edcorreamo/Mocap/Esquematico/Esquematico_completo_page-0001.jpg

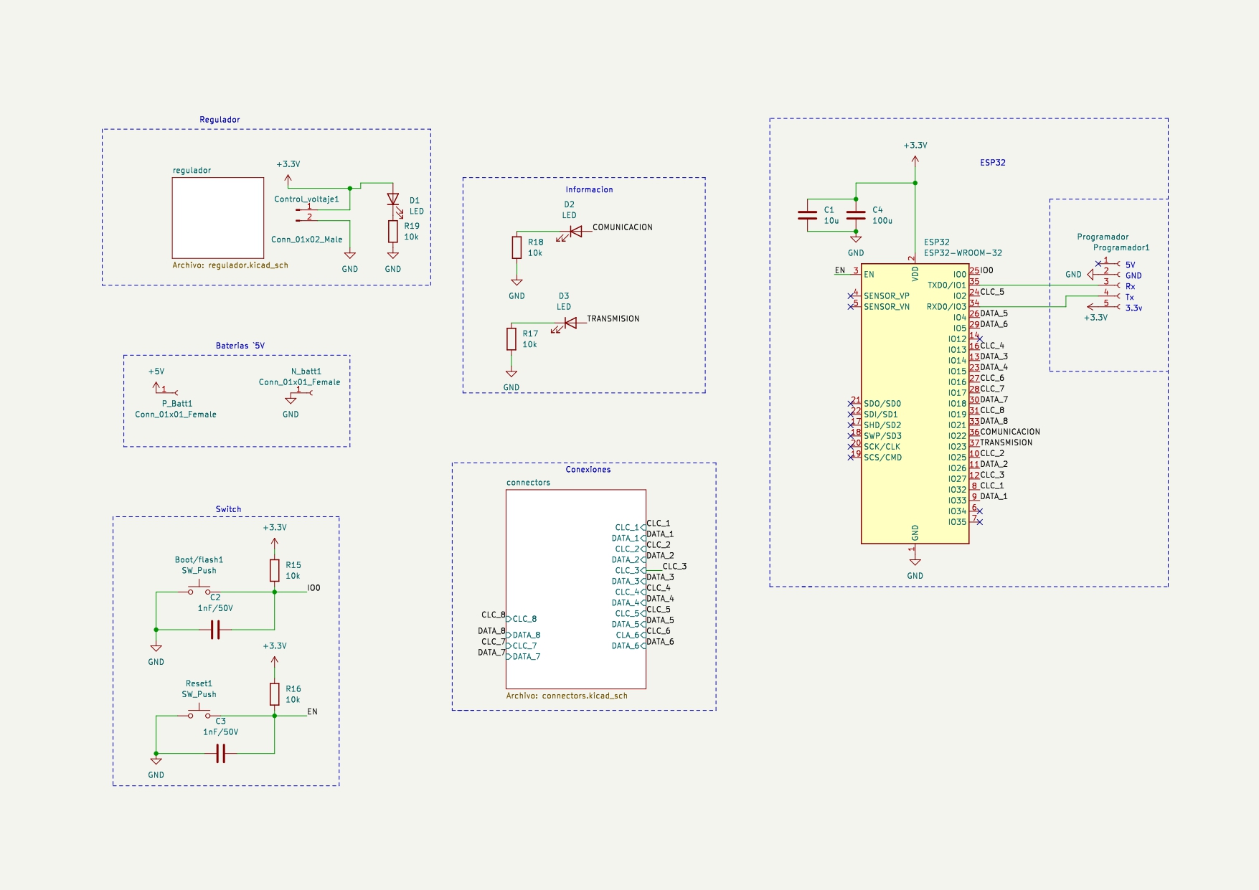
Esquematico/Esquematico_completo_page-0001.jpg
