edcorreamo/Mocap/Esquematico/Esquematico_completo_page-0002.jpg

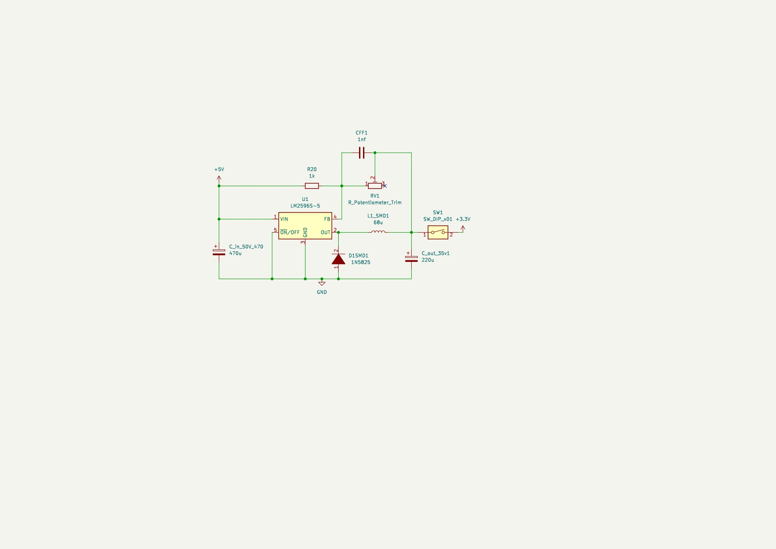
Esquematico/Esquematico_completo_page-0002.jpg
