edcorreamo/Mocap/Esquematico/Esquematico_completo_page-0003.jpg

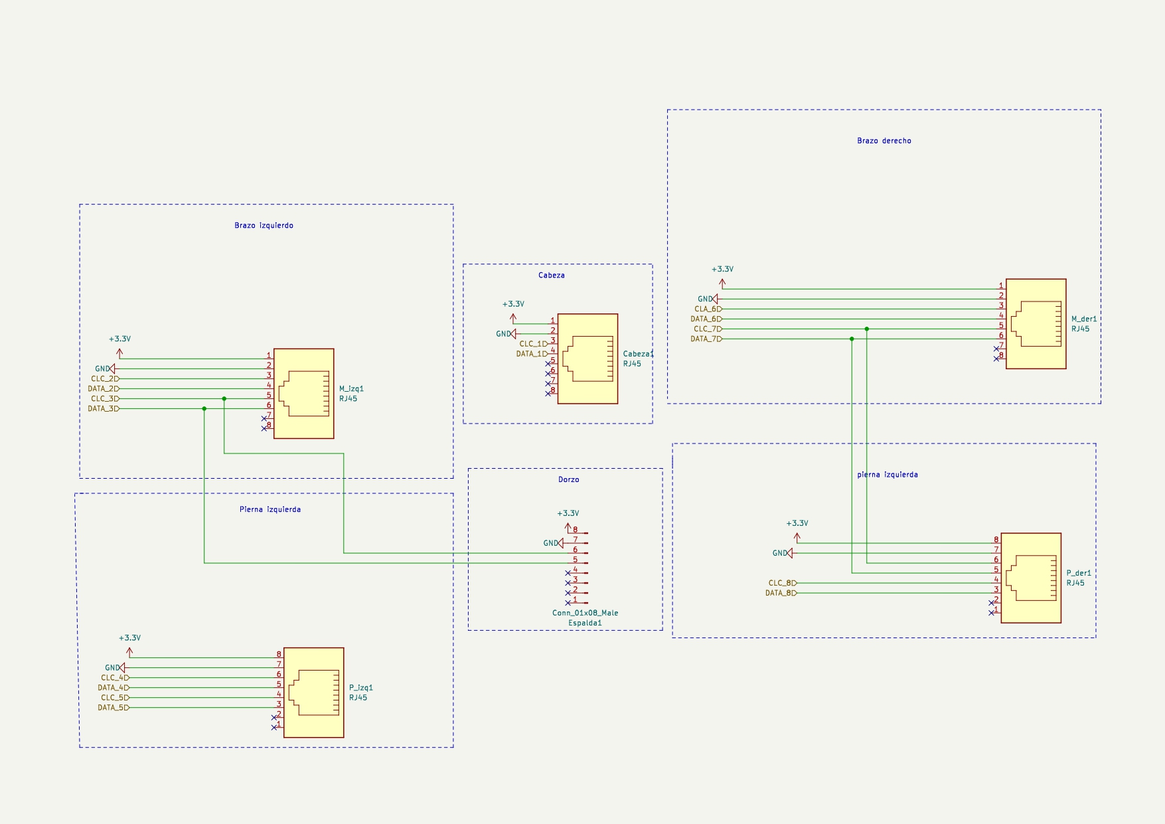
Esquematico/Esquematico_completo_page-0003.jpg
