edcorreamo/Mocap/imagenes/Base2.JPG

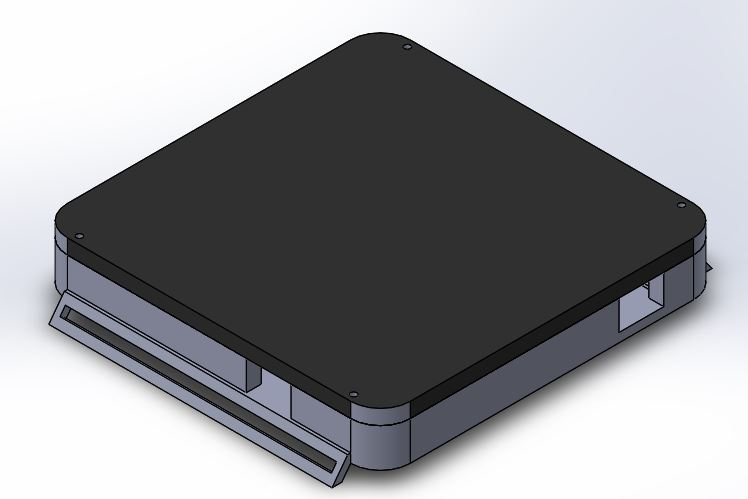
imagenes/Base2.JPG
