edcorreamo/Mocap/imagenes/Base.JPG

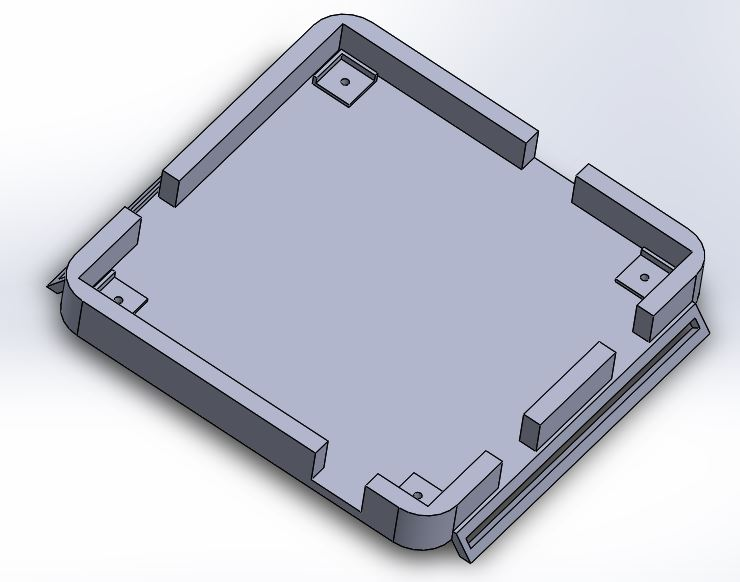
imagenes/Base.JPG
