edcorreamo/Mocap/imagenes/conector.PNG

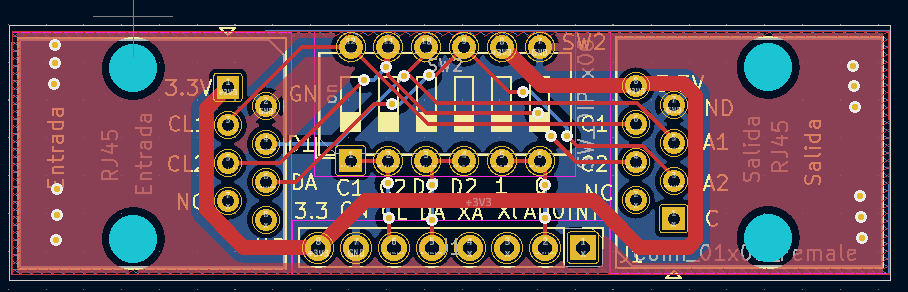
imagenes/conector.PNG
