edcorreamo/Mocap/imagenes/conector_2_3D.PNG

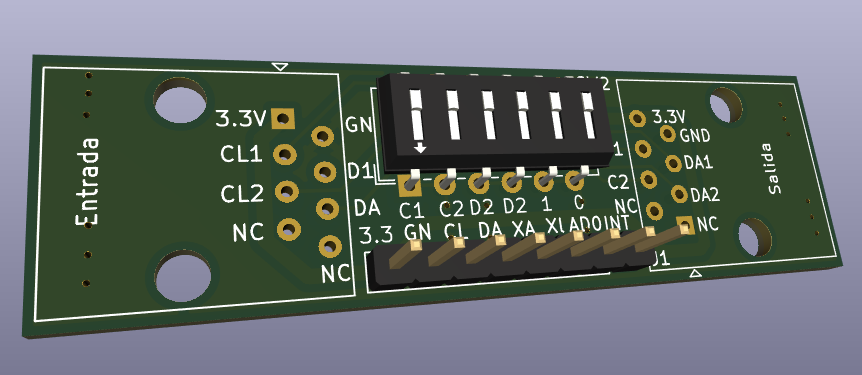
imagenes/conector_2_3D.PNG
