edcorreamo/Mocap/imagenes/cuerpo_humano_bus.JPG

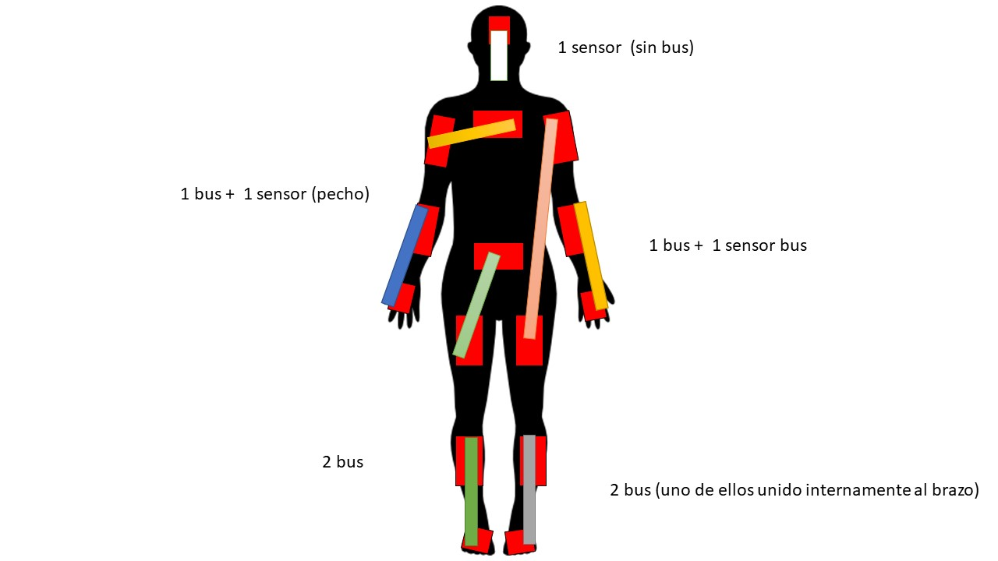
imagenes/cuerpo_humano_bus.JPG
