edcorreamo/Mocap/imagenes/cuerpo_humano_definición.JPG

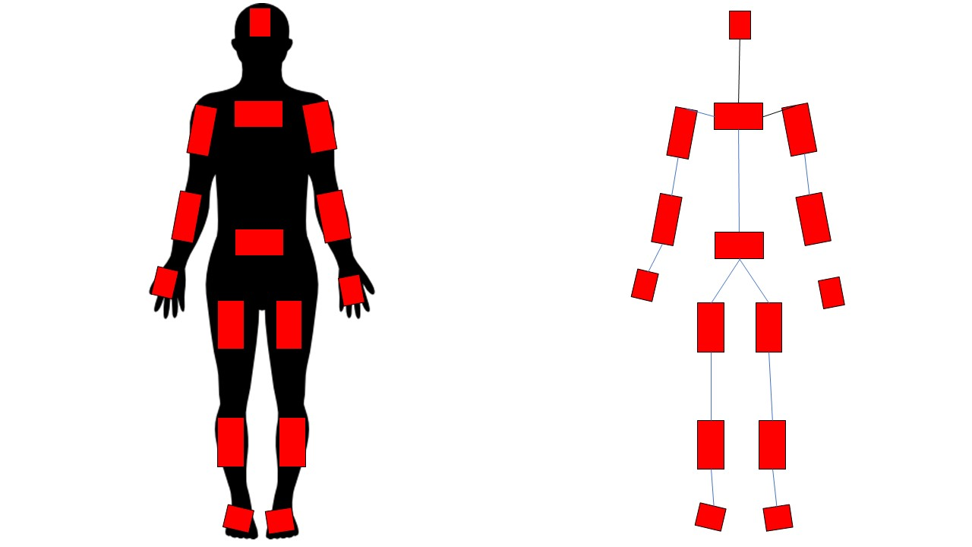
imagenes/cuerpo_humano_definición.JPG
