edcorreamo/Mocap/imagenes/diagrama de bloques.png

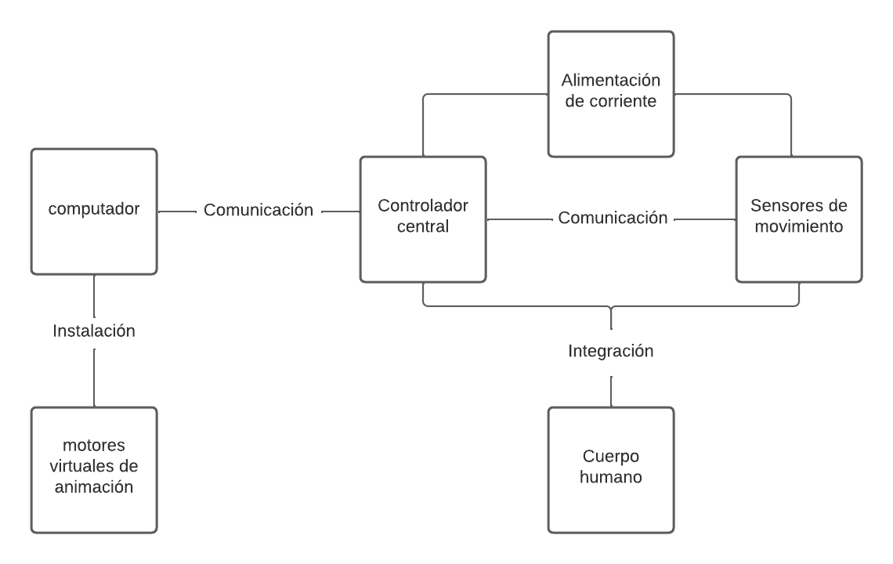
imagenes/diagrama de bloques.png
