edcorreamo/Mocap/imagenes/DiagramaMain.jpg

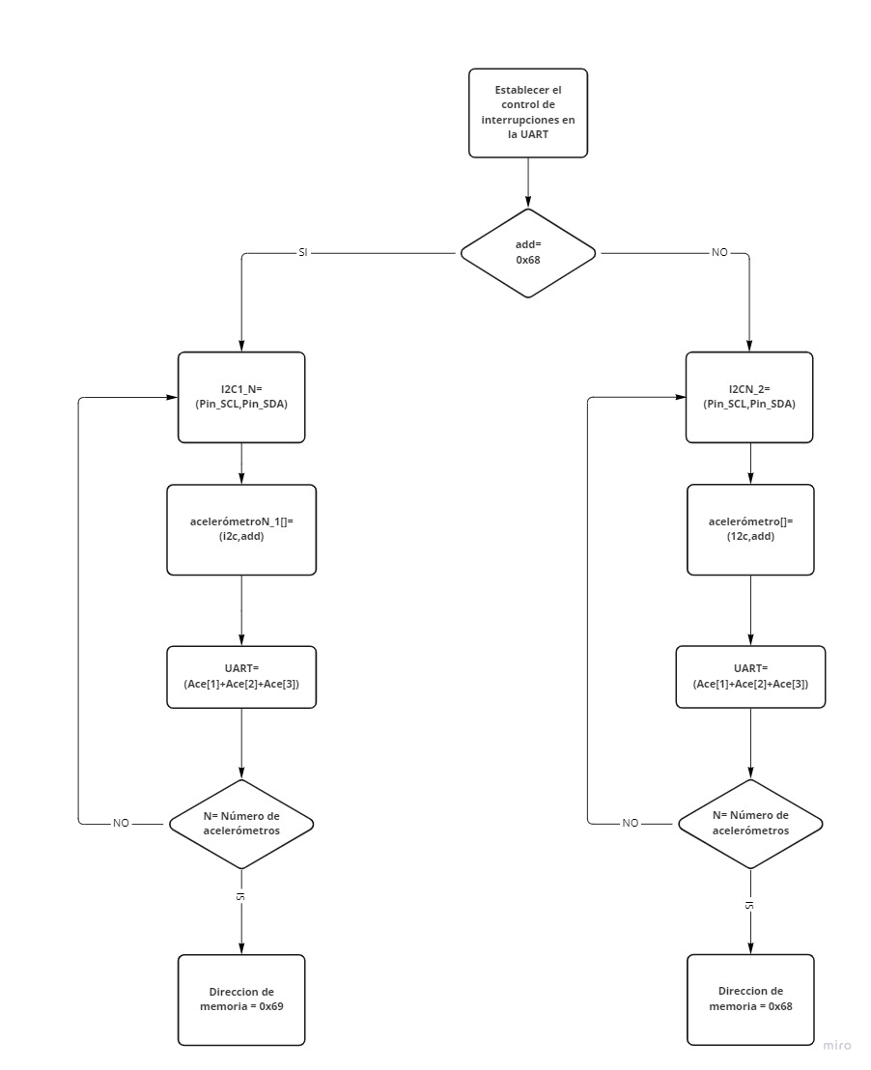
imagenes/DiagramaMain.jpg
