edcorreamo/Mocap/imagenes/DIP.jpg

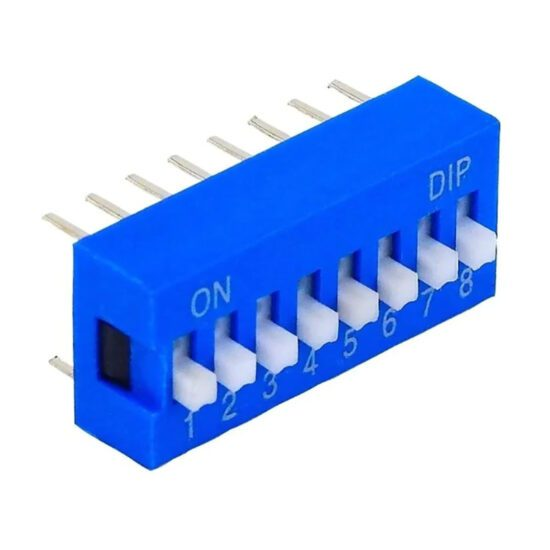
imagenes/DIP.jpg
