edcorreamo/Mocap/imagenes/entornos_virtuales.PNG

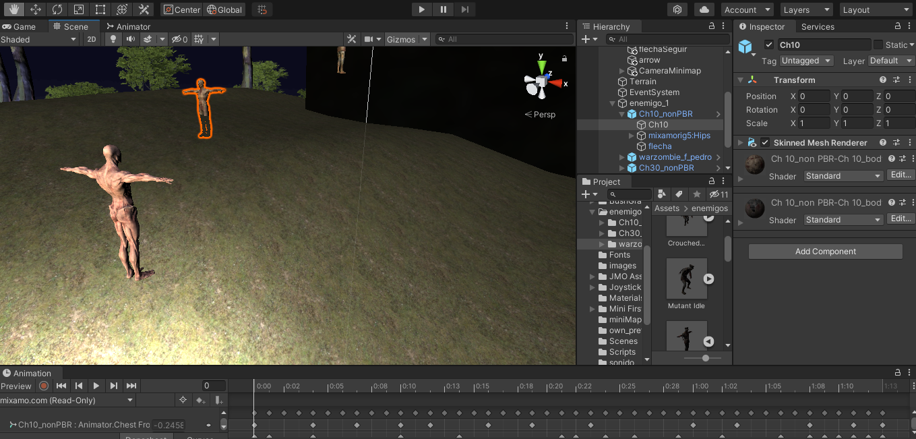
imagenes/entornos_virtuales.PNG
