edcorreamo/Mocap/imagenes/Esquematico_Completo.JPG

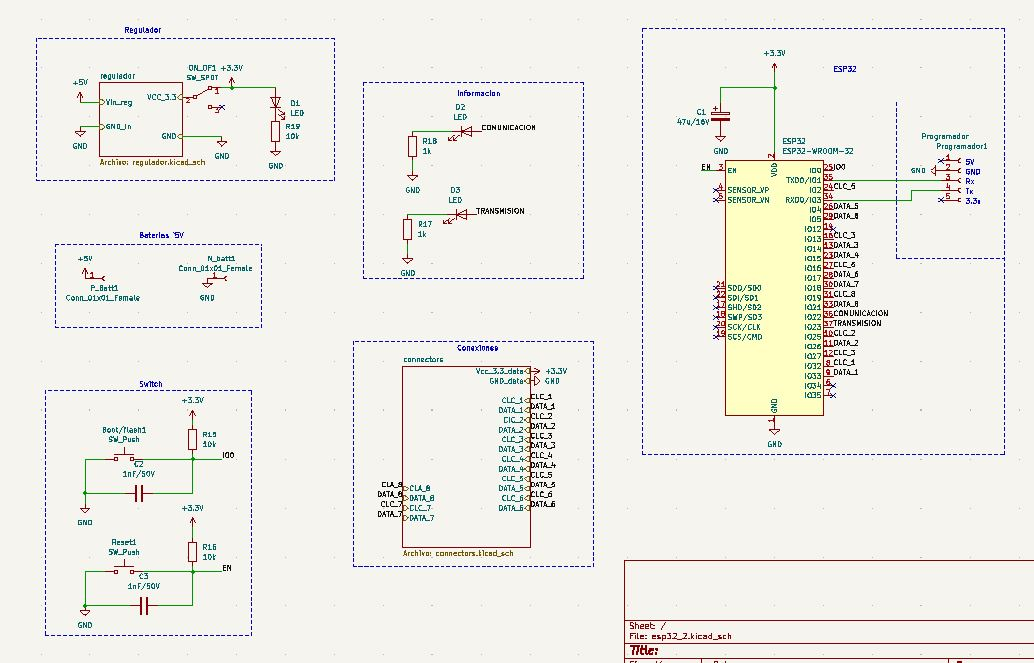
imagenes/Esquematico_Completo.JPG
