edcorreamo/Mocap/imagenes/funcionamiento_dedos.PNG

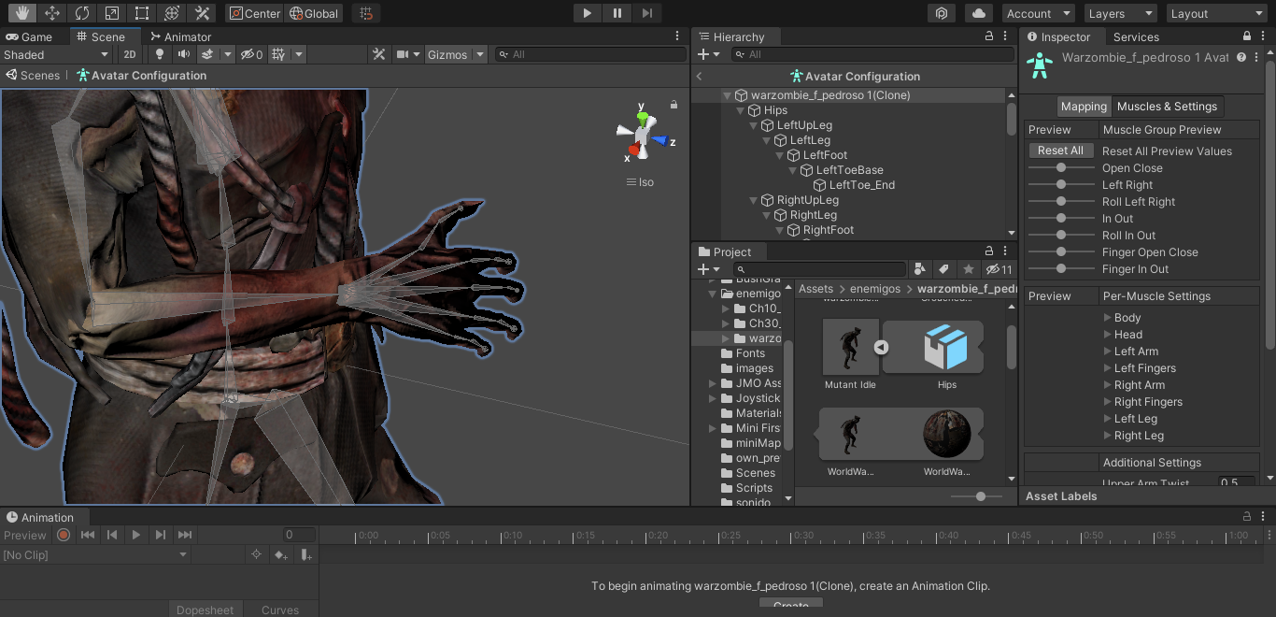
imagenes/funcionamiento_dedos.PNG
