edcorreamo/Mocap/imagenes/gestos.jpg

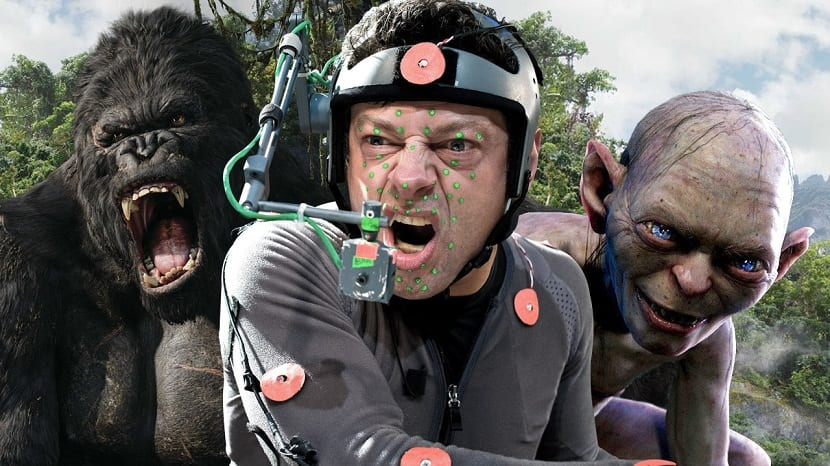
imagenes/gestos.jpg
