edcorreamo/Mocap/imagenes/mocap 1 Ejemplo.jpg

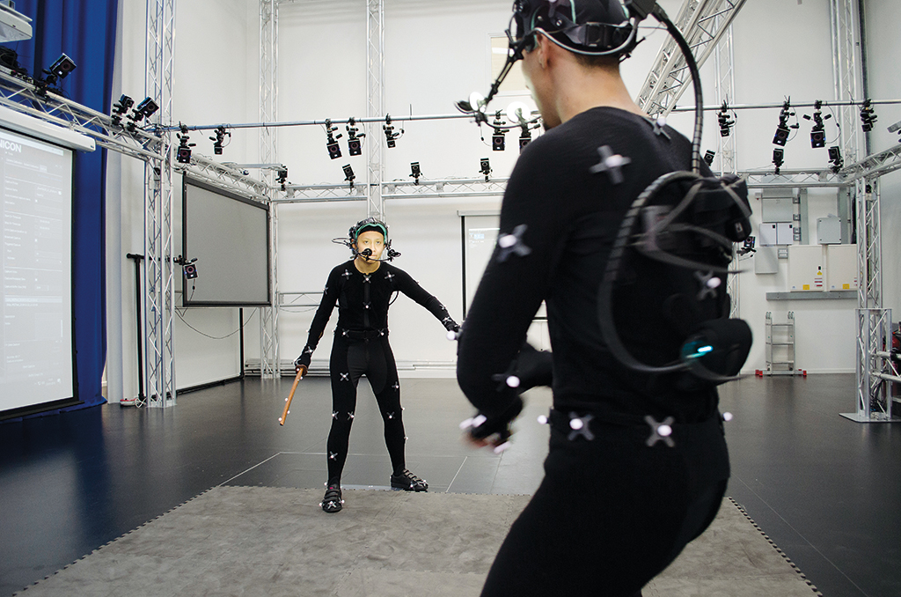
imagenes/mocap 1 Ejemplo.jpg
