edcorreamo/Mocap/imagenes/modulo_panel.PNG

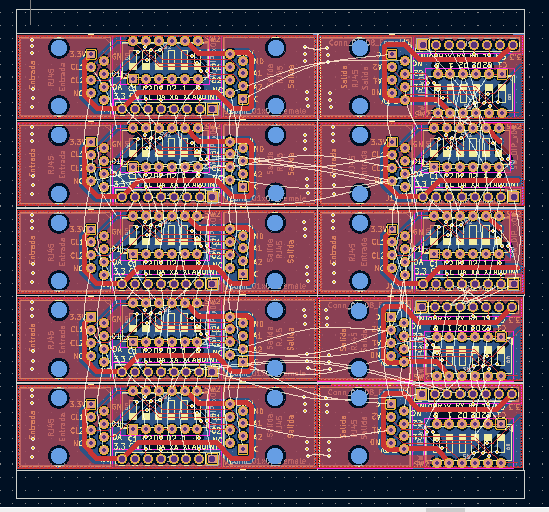
imagenes/modulo_panel.PNG
