edcorreamo/Mocap/imagenes/mpuDS2.JPG

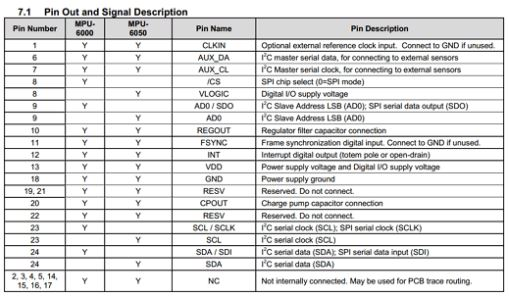
imagenes/mpuDS2.JPG
