edcorreamo/Mocap/imagenes/N.png

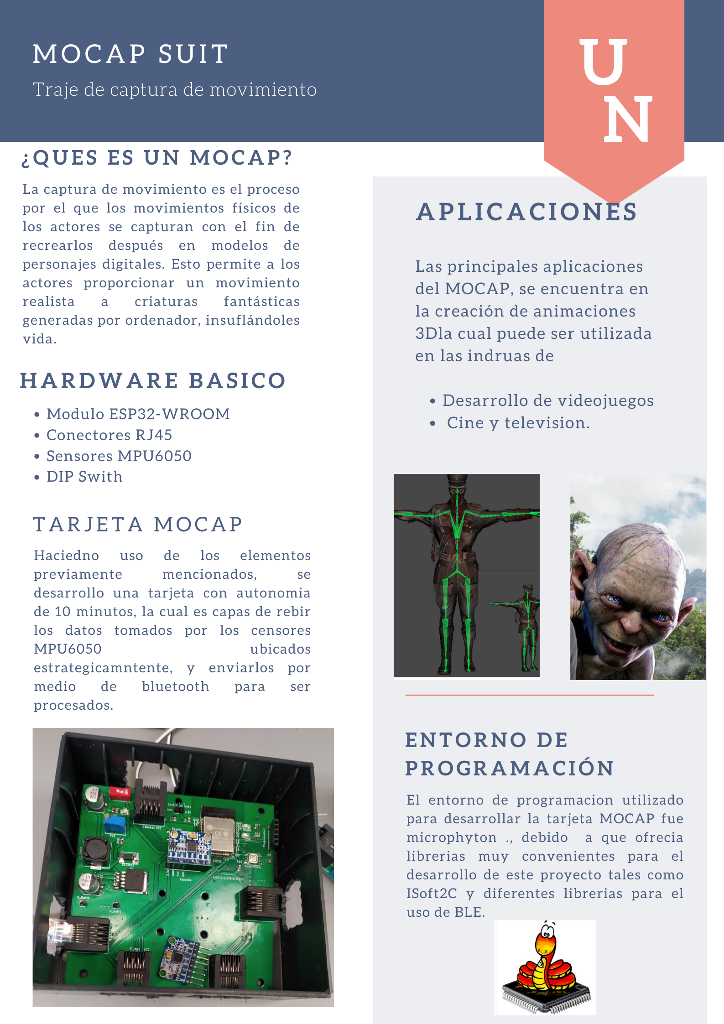
imagenes/N.png
