edcorreamo/Mocap/imagenes/núcleo_central.PNG

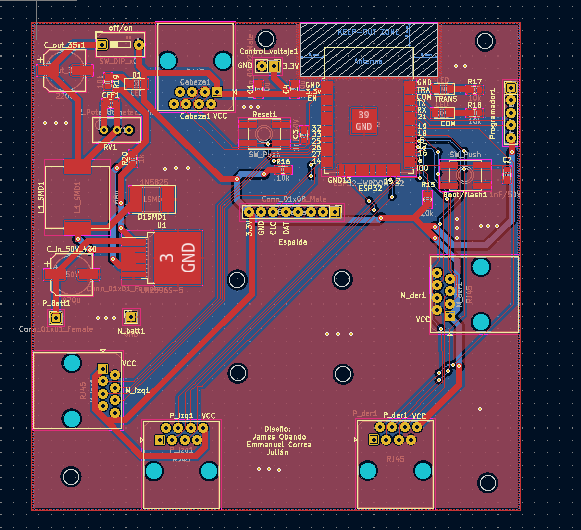
imagenes/núcleo_central.PNG
