edcorreamo/Mocap/imagenes/núcleo_central_3d.PNG

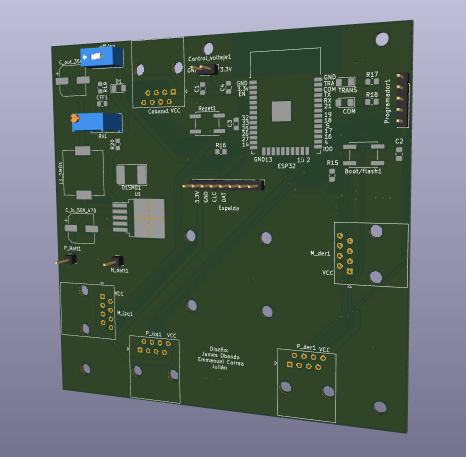
imagenes/núcleo_central_3d.PNG
