edcorreamo/Mocap/imagenes/panel_3D.PNG

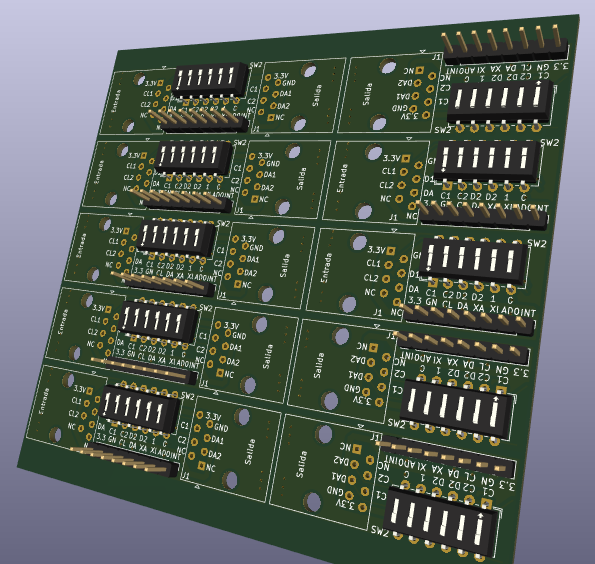
imagenes/panel_3D.PNG
