edcorreamo/Mocap/imagenes/PC.JPG

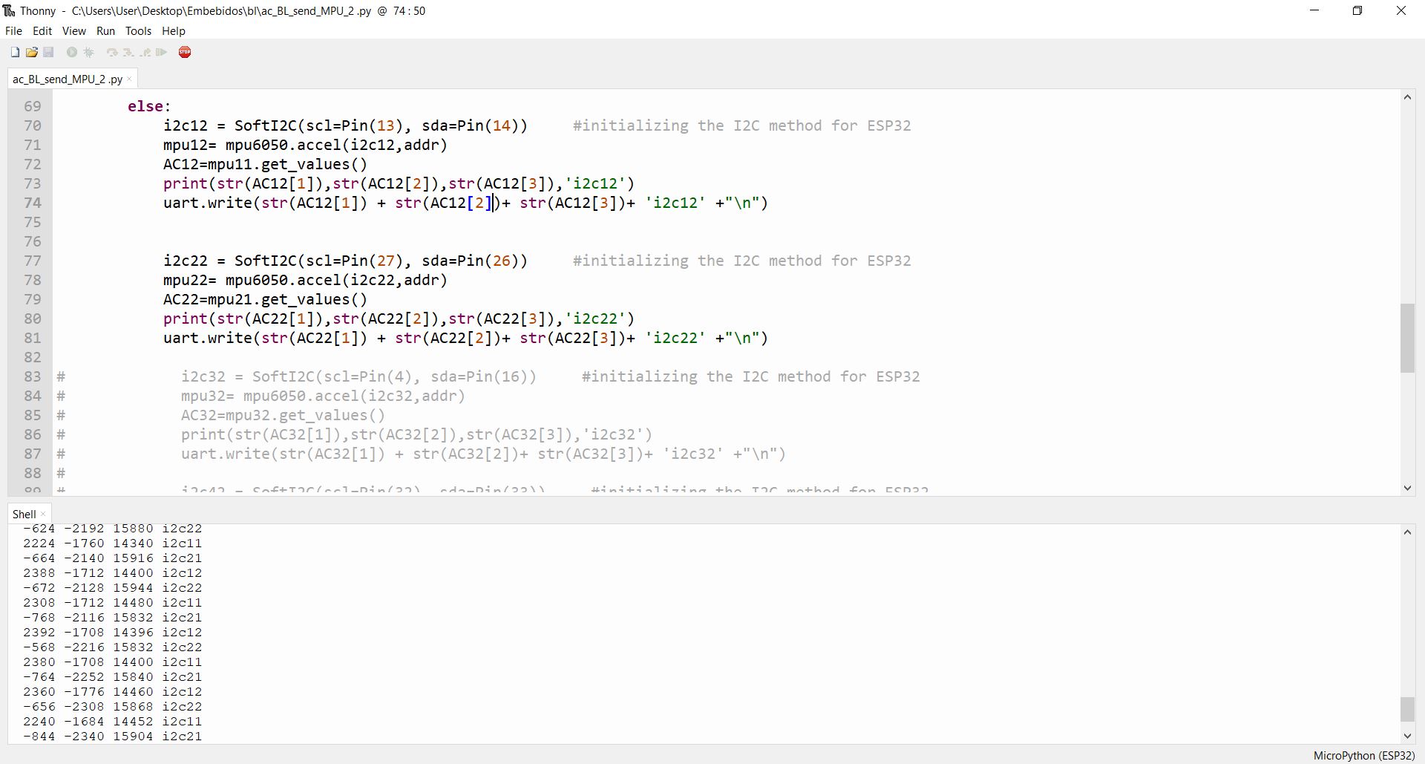
imagenes/PC.JPG
