edcorreamo/Mocap/imagenes/placa.PNG

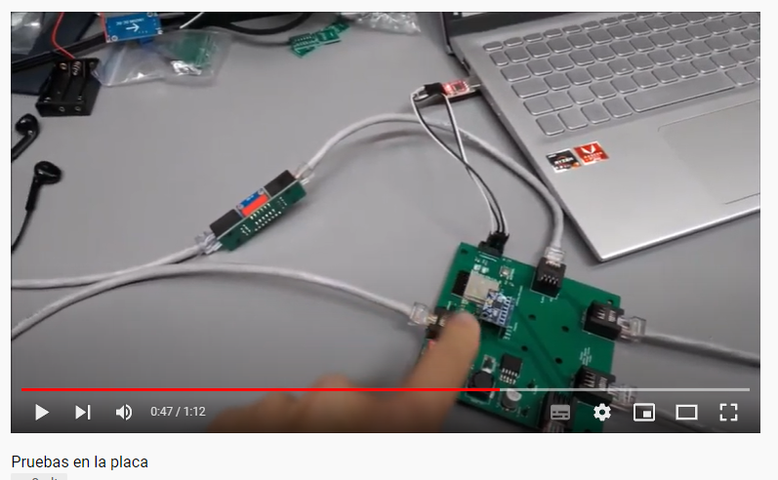
imagenes/placa.PNG
