edcorreamo/Mocap/imagenes/Presentation1.jpg

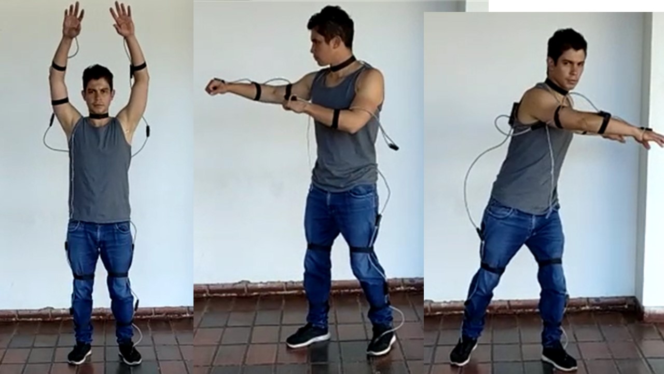
imagenes/Presentation1.jpg
