edcorreamo/Mocap/imagenes/Presentation2.jpg

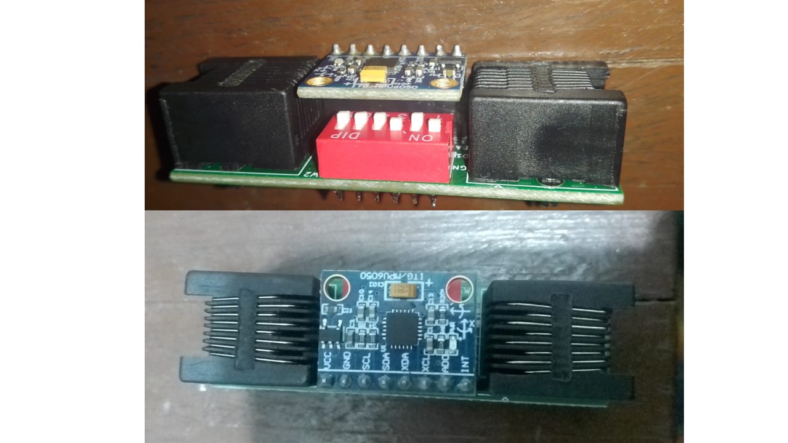
imagenes/Presentation2.jpg
