edcorreamo/Mocap/imagenes/prototipo.jpeg

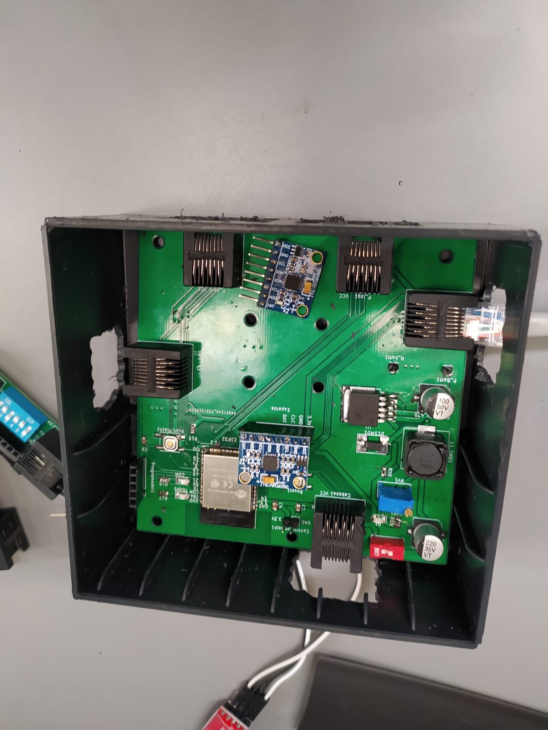
imagenes/prototipo.jpeg
