edcorreamo/Mocap/imagenes/regulador.PNG

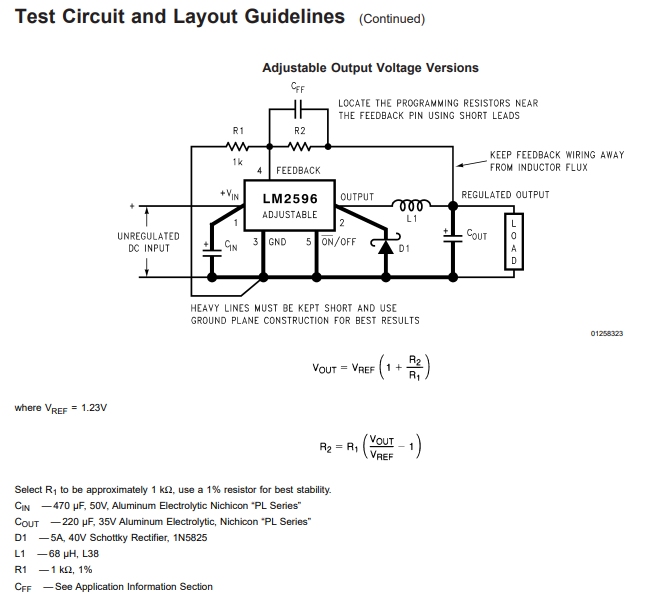
imagenes/regulador.PNG
