edcorreamo/Mocap/imagenes/RRJ45.jpg

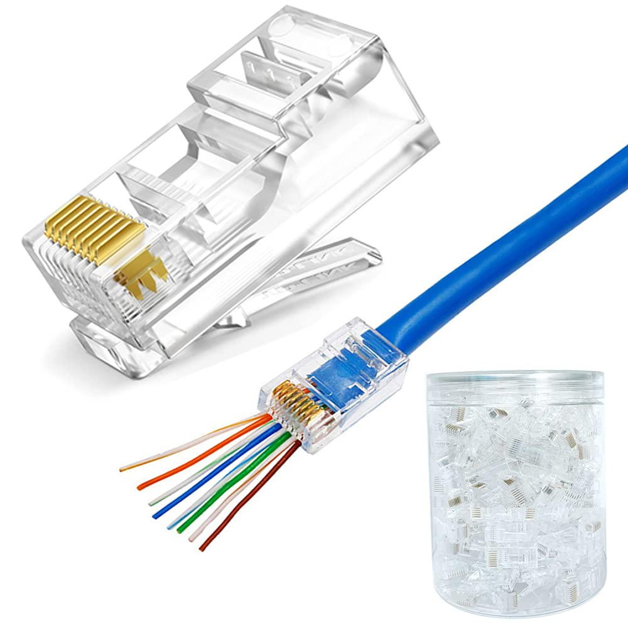
imagenes/RRJ45.jpg
