edcorreamo/Mocap/imagenes/video.PNG

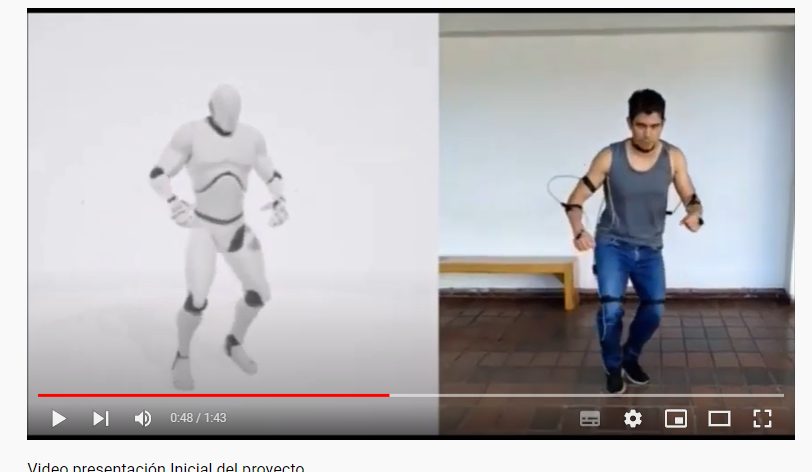
imagenes/video.PNG
