edcorreamo/Mocap/imagenes/Montaje.jpg

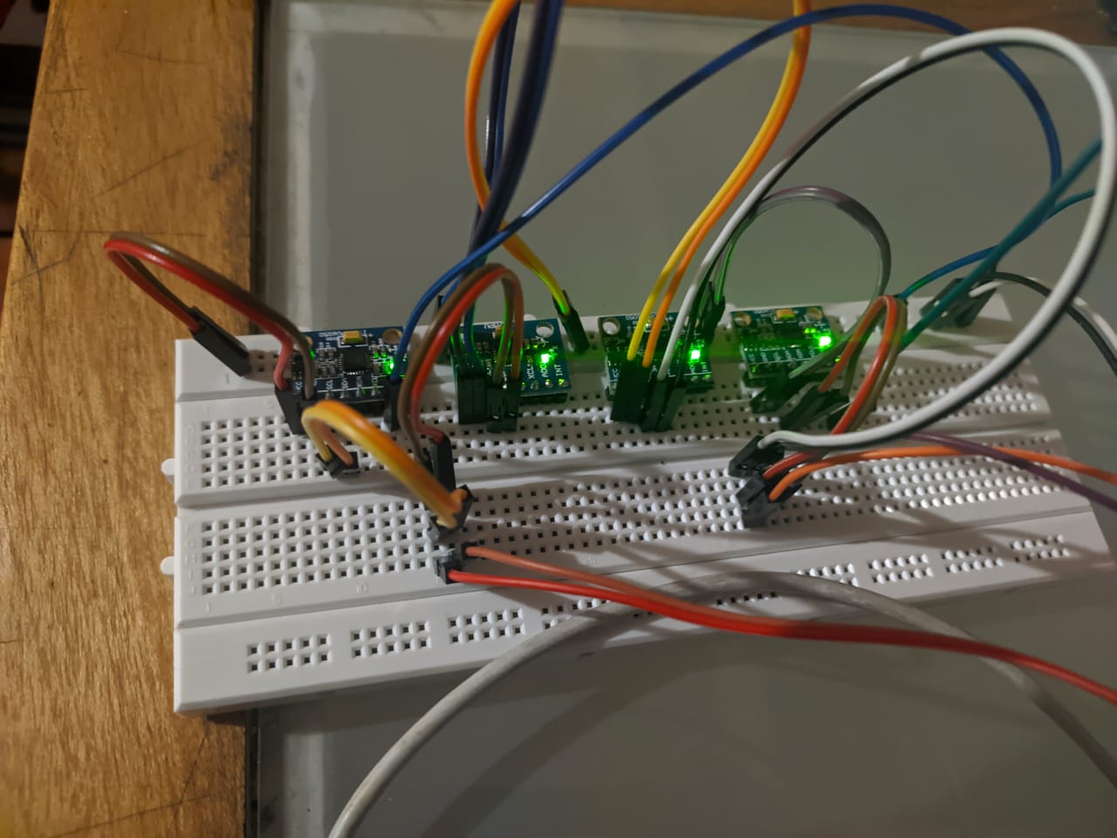
imagenes/Montaje.jpg
