edcorreamo/Mocap/imagenes/bl_prueba.jpg

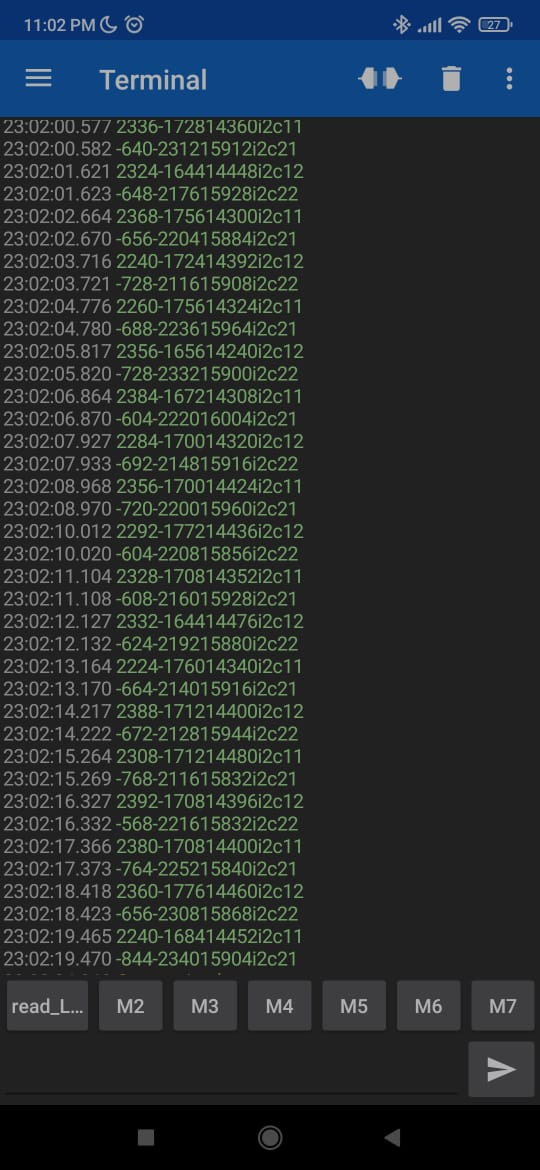
imagenes/bl_prueba.jpg
