edcorreamo/Mocap/imagenes/P1_resultados.JPG

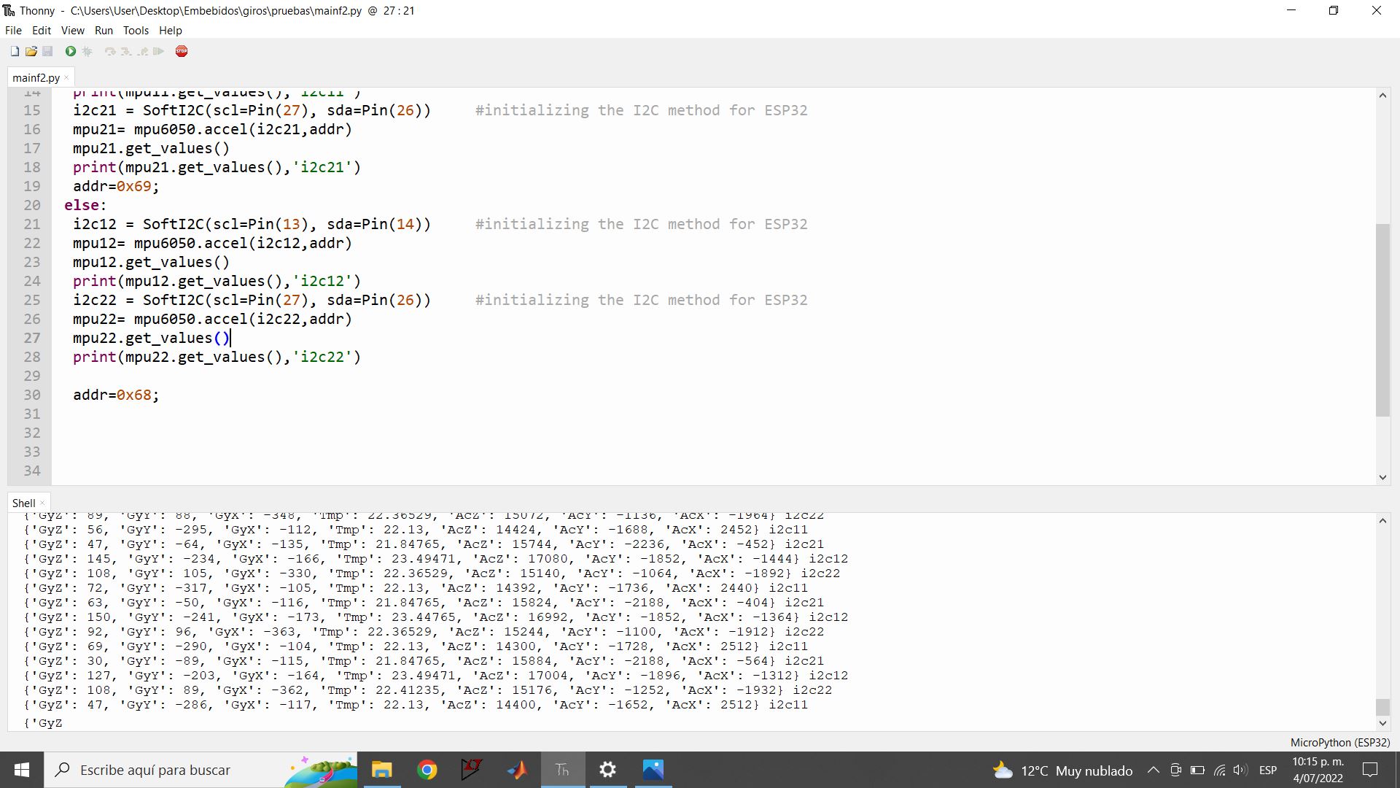
imagenes/P1_resultados.JPG
